jpskenn/Unison/assets/readme/IMG_2472.jpeg

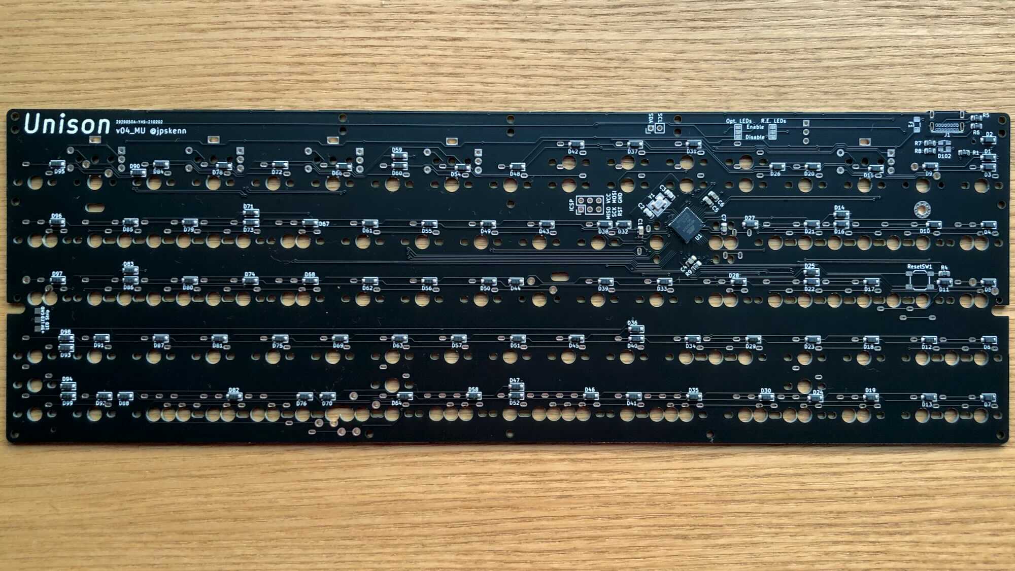
assets/readme/IMG_2472.jpeg
