jpskenn/Unison/assets/readme/IMG_2669.jpeg

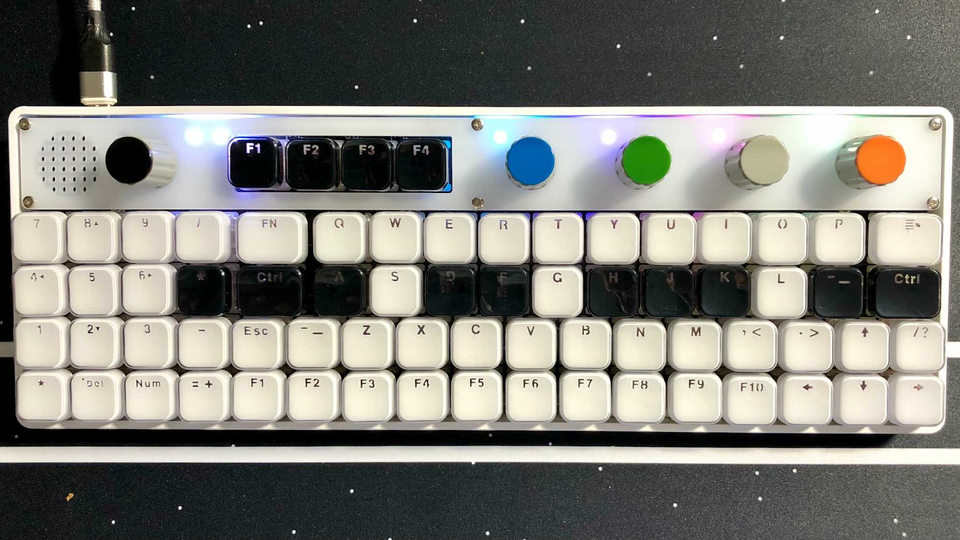
assets/readme/IMG_2669.jpeg
