jpskenn/Unison/assets/readme/IMG_2684.jpeg

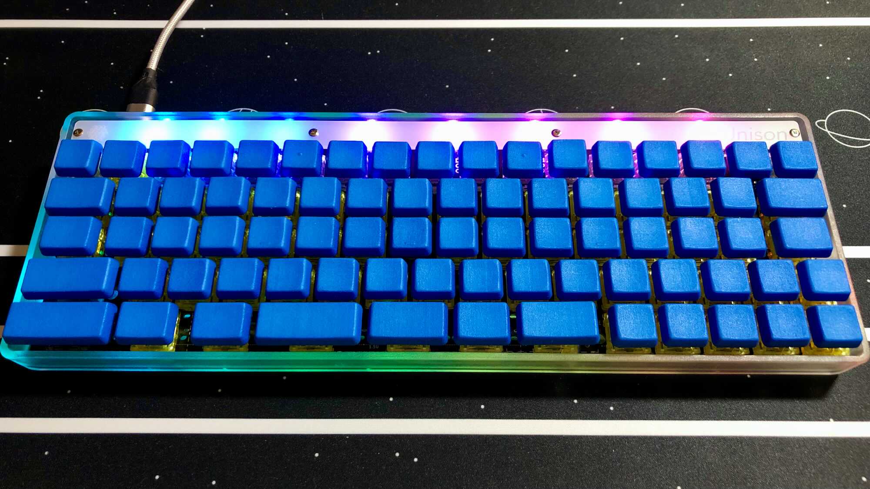
assets/readme/IMG_2684.jpeg
