jpskenn/Unison/assets/readme/layout_music.png

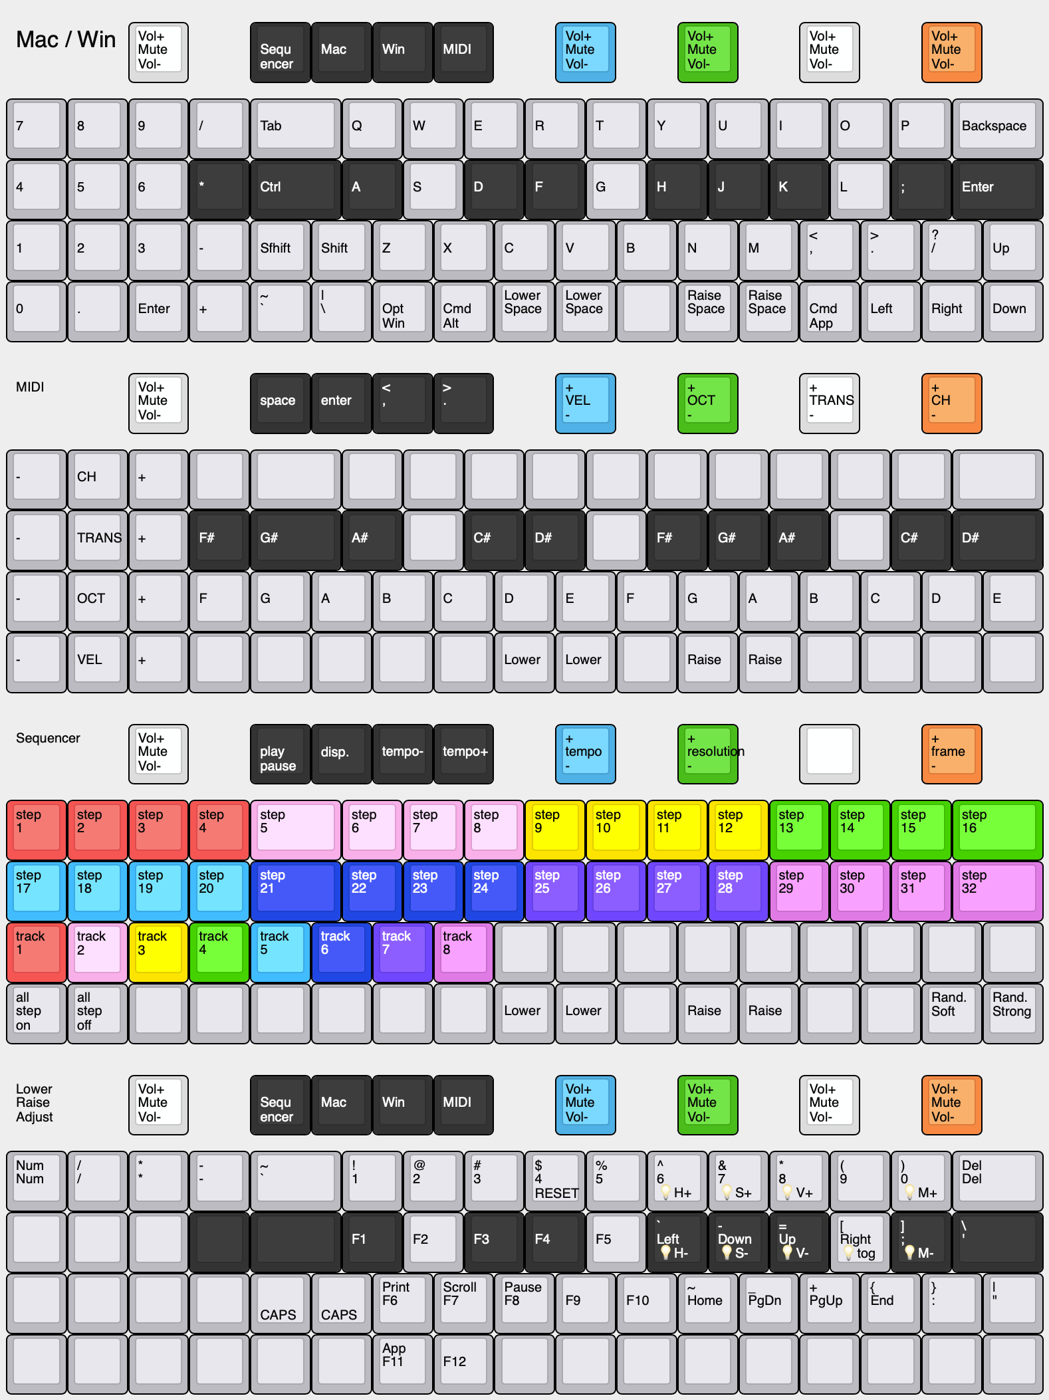
assets/readme/layout_music.png
