jpskenn/Unison/assets/readme/layout_terminal_style_variant.png

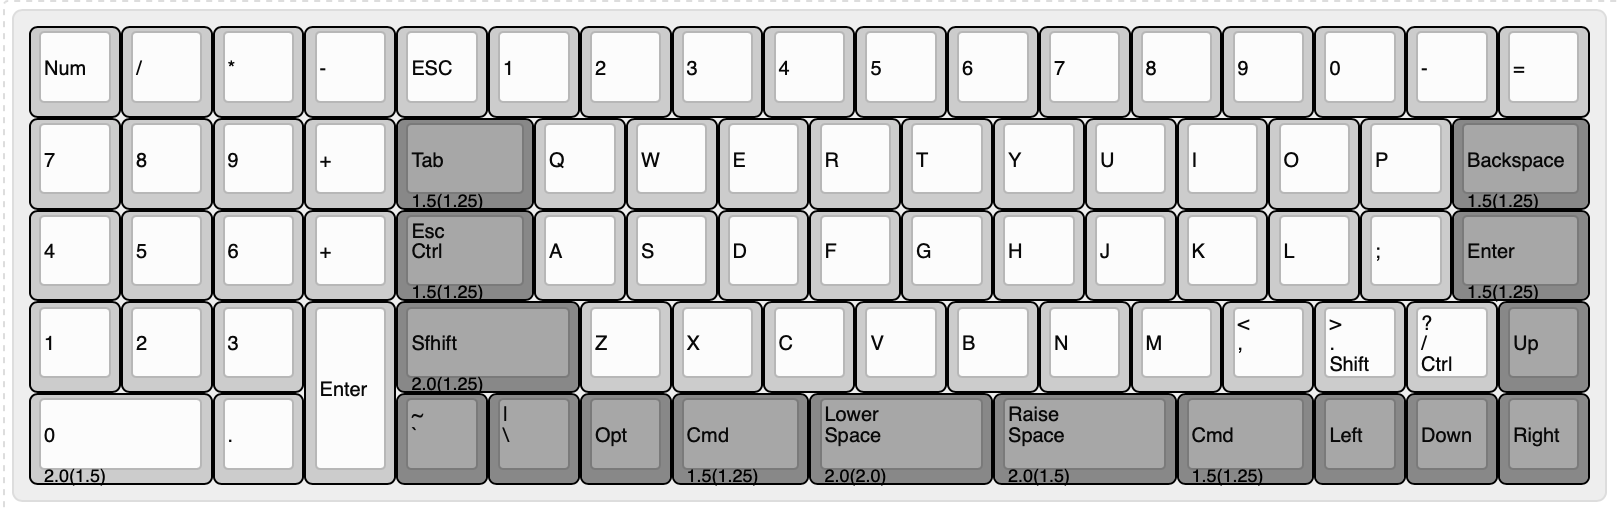
assets/readme/layout_terminal_style_variant.png
