jpskenn/Unison/assets/readme/layout_via.png

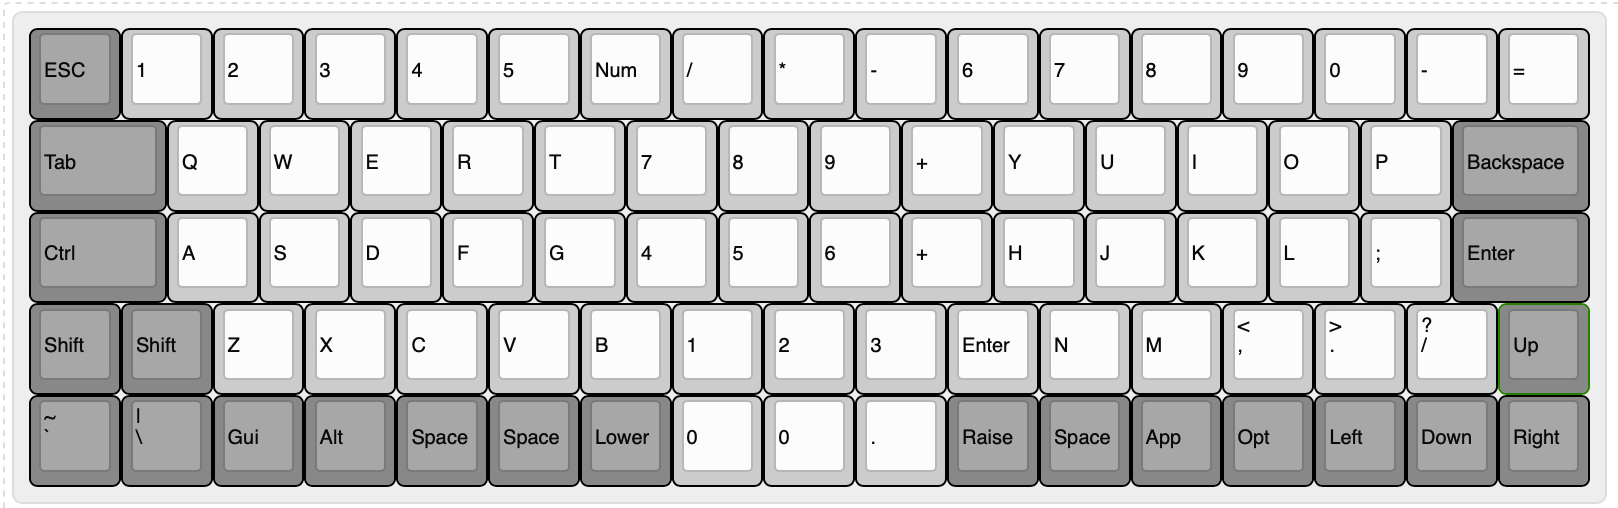
assets/readme/layout_via.png
