jpskenn/Unison/Others/Booth商品写真/v04 試作版/DSC_7390.jpeg

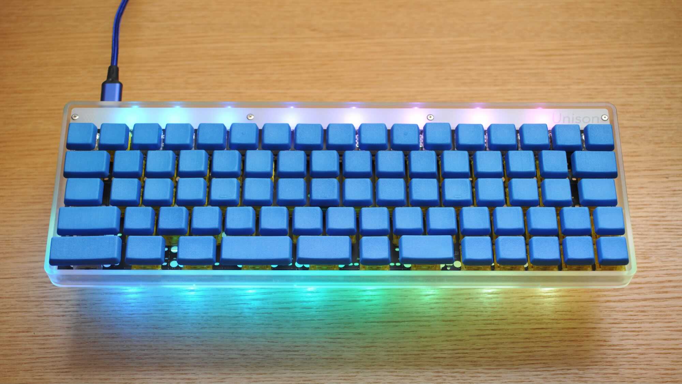
Others/Booth商品写真/v04 試作版/DSC_7390.jpeg
