jpskenn/Unison/Others/シーケンサー操作ガイドキャプション/02_1.png

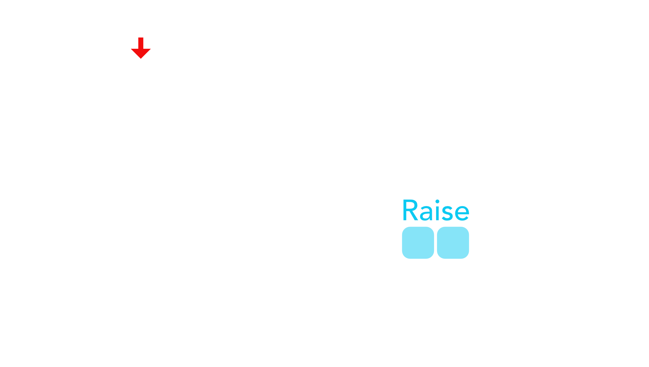
Others/シーケンサー操作ガイドキャプション/02_1.png
