jpskenn/Unison/Others/シーケンサー操作ガイドキャプション/02_2.png

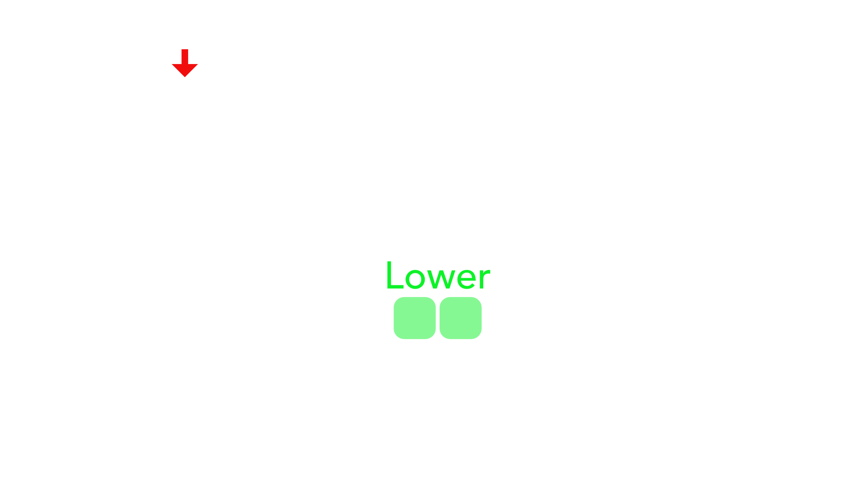
Others/シーケンサー操作ガイドキャプション/02_2.png
