jpskenn/Unison/Others/シーケンサー操作ガイドキャプション/02_3.png

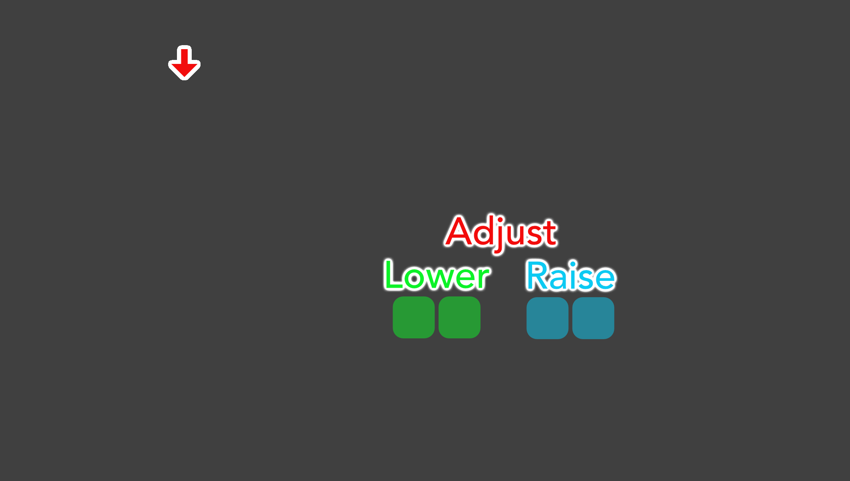
Others/シーケンサー操作ガイドキャプション/02_3.png
