jpskenn/Unison/Others/シーケンサー操作ガイドキャプション/02_4.png

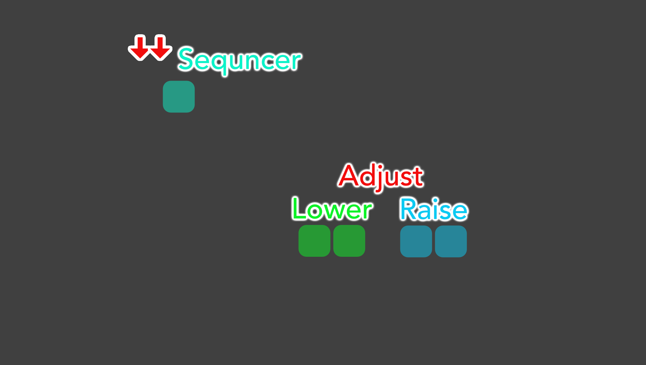
Others/シーケンサー操作ガイドキャプション/02_4.png
