jpskenn/Unison/Others/シーケンサー操作ガイドキャプション/04_60.png

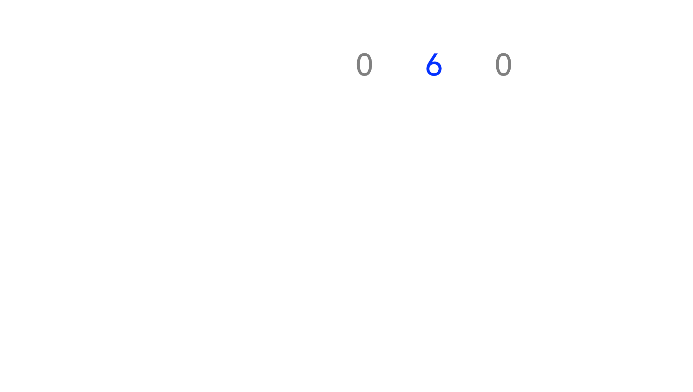
Others/シーケンサー操作ガイドキャプション/04_60.png
