jpskenn/Unison/Others/シーケンサー操作ガイドキャプション/05_1.png

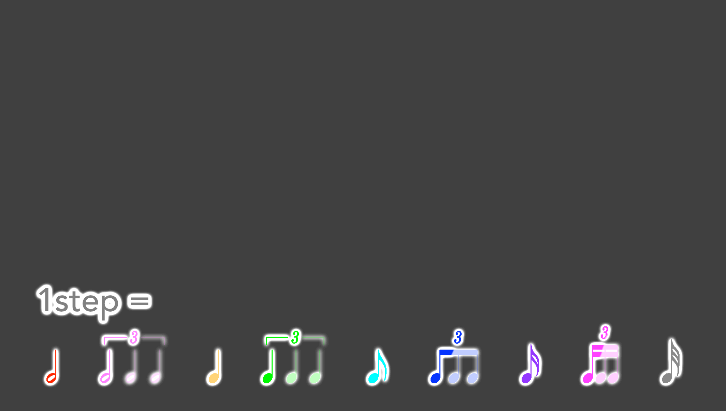
Others/シーケンサー操作ガイドキャプション/05_1.png
