jpskenn/Unison/Others/シーケンサー操作ガイドキャプション/06_1.png

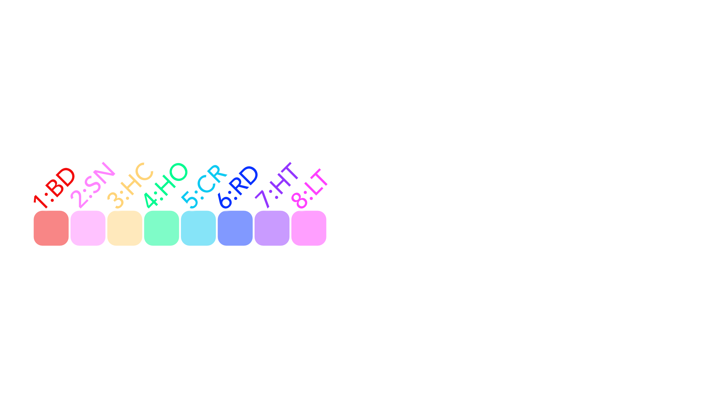
Others/シーケンサー操作ガイドキャプション/06_1.png
