jpskenn/Unison/Others/シーケンサー操作ガイドキャプション/06_2.png

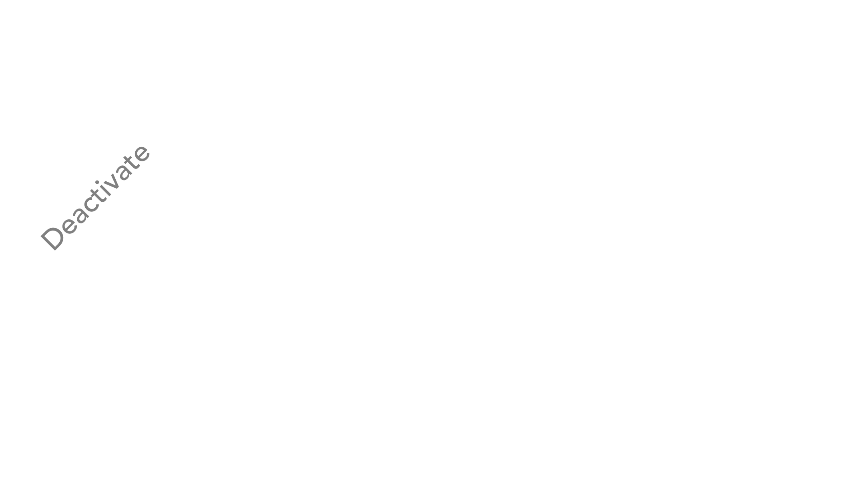
Others/シーケンサー操作ガイドキャプション/06_2.png
