jpskenn/Unison/Others/シーケンサー操作ガイドキャプション/07_1.png

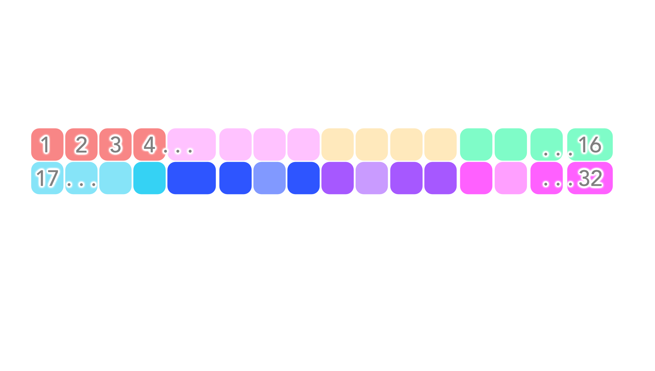
Others/シーケンサー操作ガイドキャプション/07_1.png
