jpskenn/Unison/Others/シーケンサー操作ガイドキャプション/07_2.png

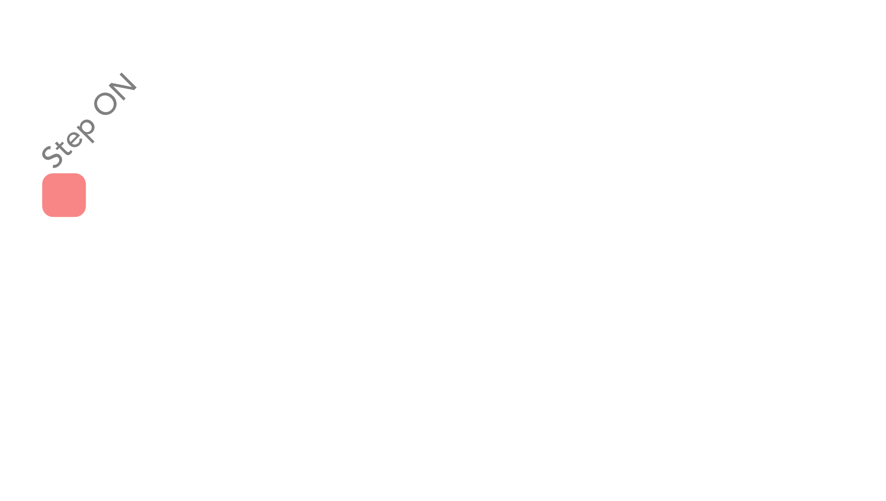
Others/シーケンサー操作ガイドキャプション/07_2.png
