jpskenn/Unison/Others/シーケンサー操作ガイドキャプション/07_5.png

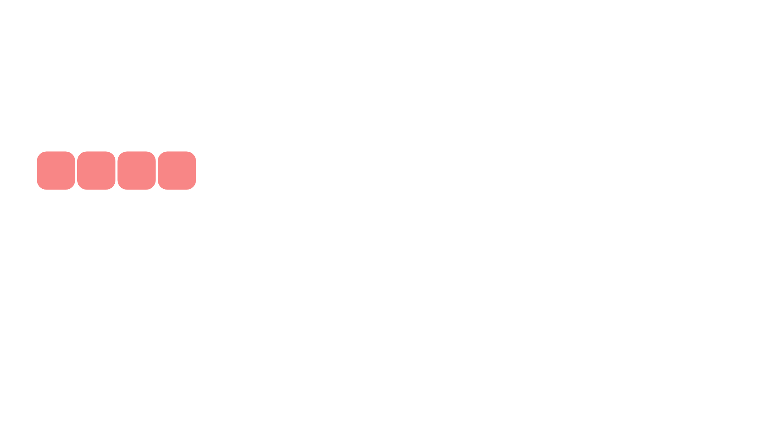
Others/シーケンサー操作ガイドキャプション/07_5.png
