jpskenn/Unison/Others/シーケンサー操作ガイドキャプション/08_2.png

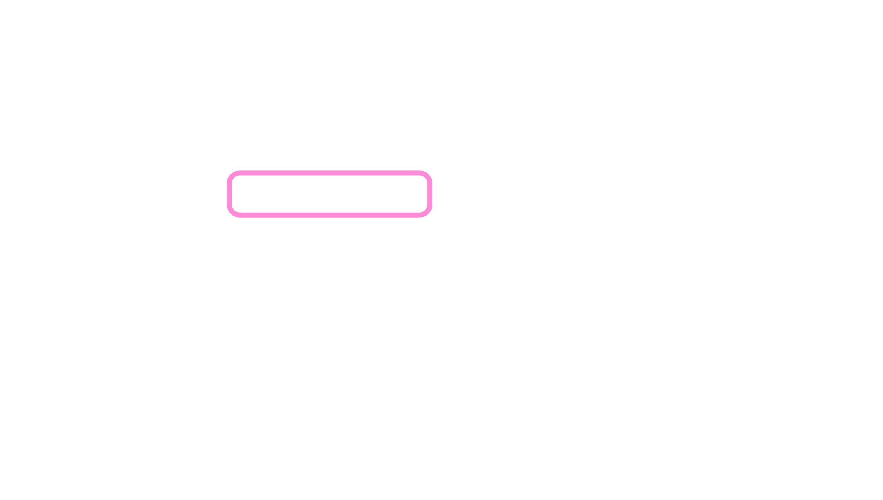
Others/シーケンサー操作ガイドキャプション/08_2.png
