jpskenn/Unison/Others/シーケンサー操作ガイドキャプション/08_3.png

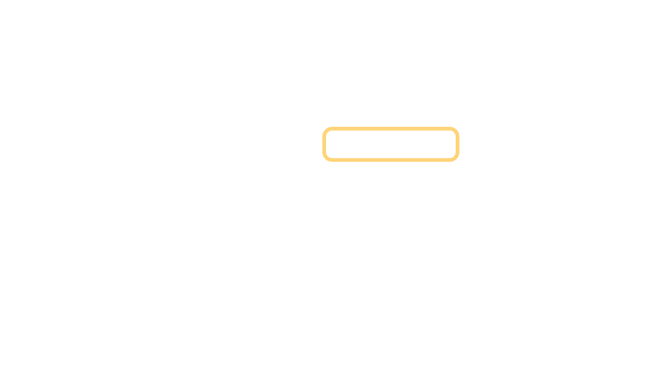
Others/シーケンサー操作ガイドキャプション/08_3.png
