jpskenn/Unison/Others/シーケンサー操作ガイドキャプション/08_4.png

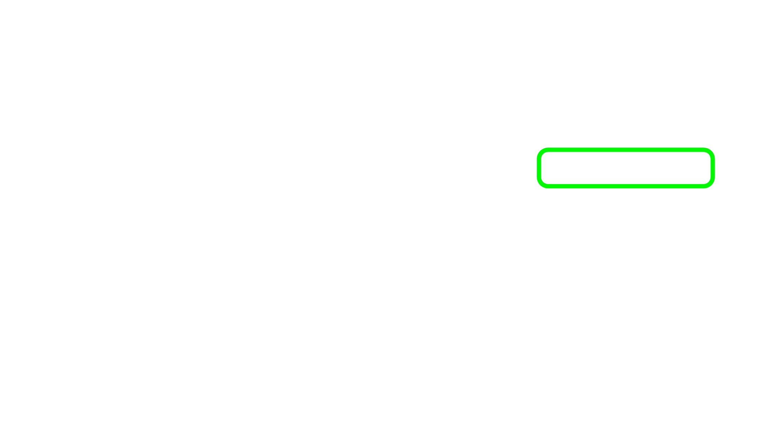
Others/シーケンサー操作ガイドキャプション/08_4.png
