jpskenn/Unison/Others/シーケンサー操作ガイドキャプション/08_5.png

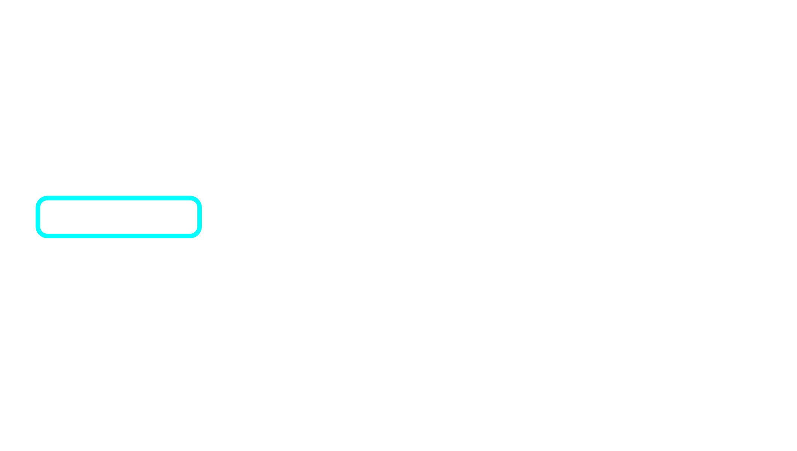
Others/シーケンサー操作ガイドキャプション/08_5.png
