jpskenn/Unison/Others/シーケンサー操作ガイドキャプション/08_7.png

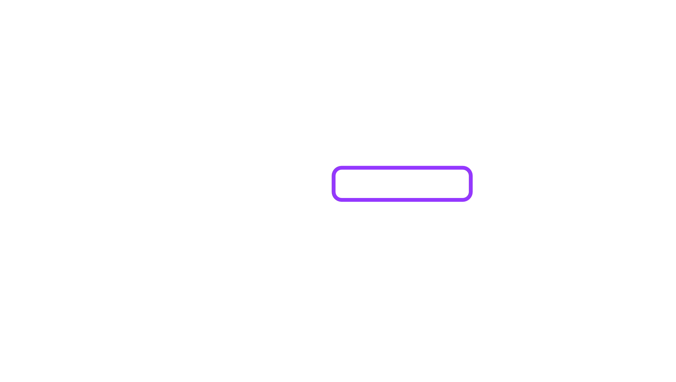
Others/シーケンサー操作ガイドキャプション/08_7.png
