jpskenn/Unison/Others/シーケンサー操作ガイドキャプション/09_1.png

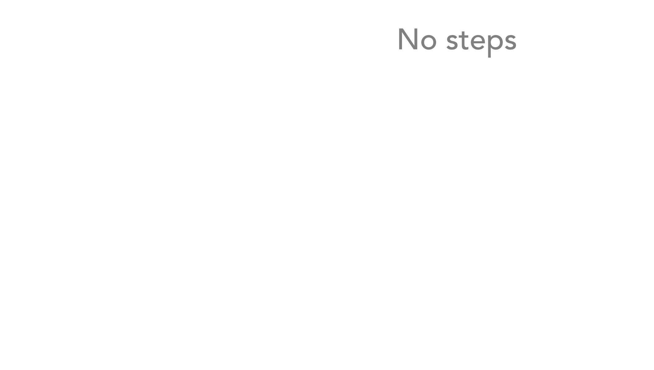
Others/シーケンサー操作ガイドキャプション/09_1.png
