jpskenn/Unison/Others/シーケンサー操作ガイドキャプション/09_4.png

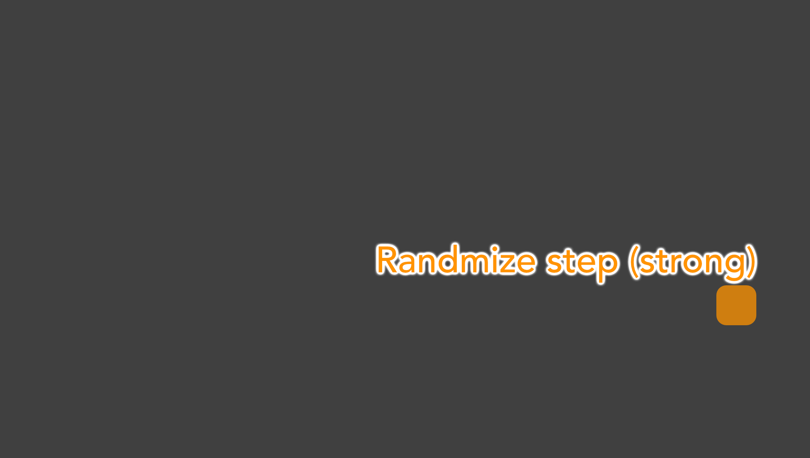
Others/シーケンサー操作ガイドキャプション/09_4.png
