jpskenn/Unison/Others/シーケンサー操作ガイドキャプション/10_1.png

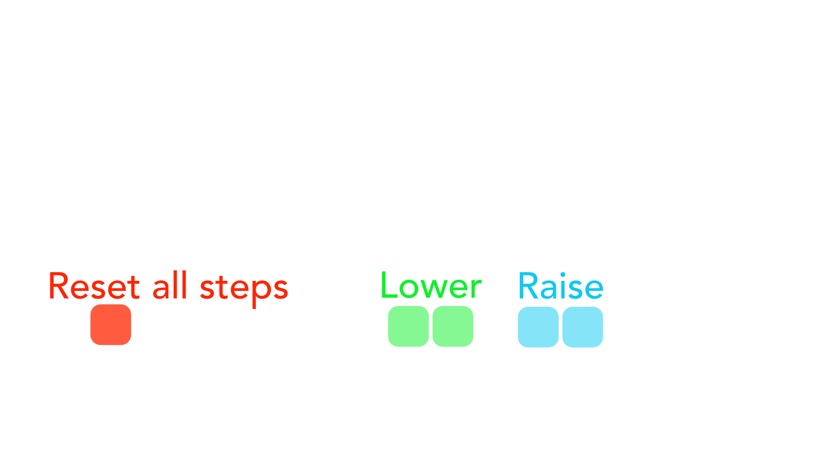
Others/シーケンサー操作ガイドキャプション/10_1.png
